rodread/DaisyKiteTurbineControl/2019-11-14_09-22-19.jpg

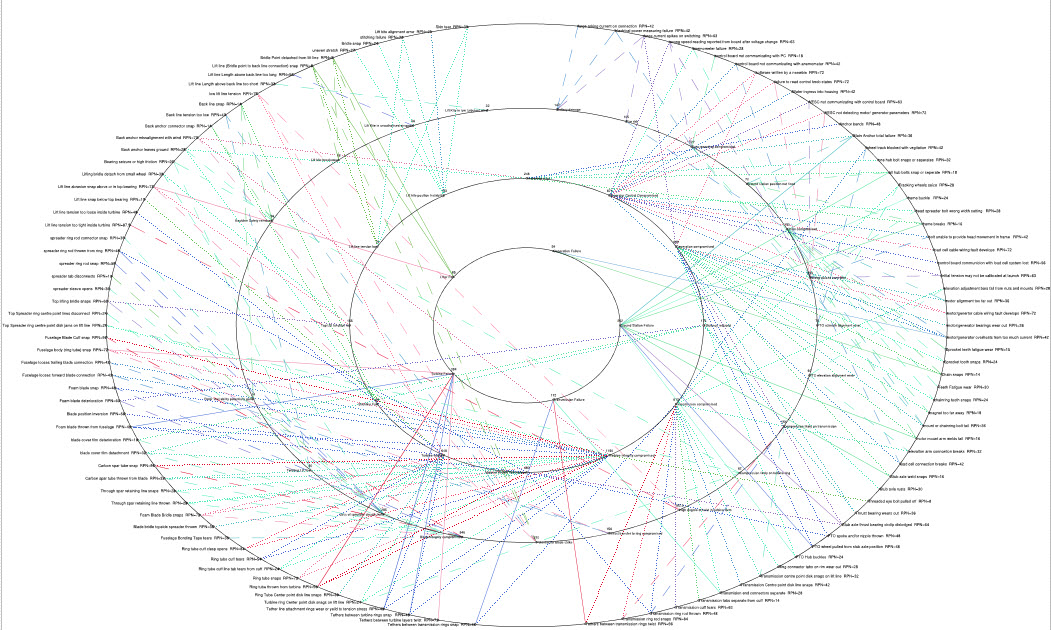
2019-11-14_09-22-19.jpg
