rodread/DaisyKiteTurbineControl/29APR20-Hexring-Tower/buffer.cpp

/*
	Copyright 2012-2014 Benjamin Vedder	benjamin@vedder.se

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
    You should have received a copy of the GNU General Public License
    along with this program.  If not, see <http://www.gnu.org/licenses/>.
    */

/*
 * buffer.c
 *
 *  Created on: 13 maj 2013
 *      Author: benjamin
 */

#include "buffer.h"

void buffer_append_int16(uint8_t* buffer, int16_t number, int32_t *index) {
	buffer[(*index)++] = number >> 8;
	buffer[(*index)++] = number;
}

void buffer_append_uint16(uint8_t* buffer, uint16_t number, int32_t *index) {
	buffer[(*index)++] = number >> 8;
	buffer[(*index)++] = number;
}

void buffer_append_int32(uint8_t* buffer, int32_t number, int32_t *index) {
	buffer[(*index)++] = number >> 24;
	buffer[(*index)++] = number >> 16;
	buffer[(*index)++] = number >> 8;
	buffer[(*index)++] = number;
}

void buffer_append_uint32(uint8_t* buffer, uint32_t number, int32_t *index) {
	buffer[(*index)++] = number >> 24;
	buffer[(*index)++] = number >> 16;
	buffer[(*index)++] = number >> 8;
	buffer[(*index)++] = number;
}

void buffer_append_float16(uint8_t* buffer, float number, float scale, int32_t *index) {
    buffer_append_int16(buffer, (int16_t)(number * scale), index);
}

void buffer_append_float32(uint8_t* buffer, float number, float scale, int32_t *index) {
    buffer_append_int32(buffer, (int32_t)(number * scale), index);
}

int16_t buffer_get_int16(const uint8_t *buffer, int32_t *index) {
	int16_t res =	((uint16_t) buffer[*index]) << 8 |
					((uint16_t) buffer[*index + 1]);
	*index += 2;
	return res;
}

uint16_t buffer_get_uint16(const uint8_t *buffer, int32_t *index) {
	uint16_t res = 	((uint16_t) buffer[*index]) << 8 |
					((uint16_t) buffer[*index + 1]);
	*index += 2;
	return res;
}

int32_t buffer_get_int32(const uint8_t *buffer, int32_t *index) {
	int32_t res =	((uint32_t) buffer[*index]) << 24 |
					((uint32_t) buffer[*index + 1]) << 16 |
					((uint32_t) buffer[*index + 2]) << 8 |
					((uint32_t) buffer[*index + 3]);
	*index += 4;
	return res;
}

uint32_t buffer_get_uint32(const uint8_t *buffer, int32_t *index) {
	uint32_t res =	((uint32_t) buffer[*index]) << 24 |
					((uint32_t) buffer[*index + 1]) << 16 |
					((uint32_t) buffer[*index + 2]) << 8 |
					((uint32_t) buffer[*index + 3]);
	*index += 4;
	return res;
}

float buffer_get_float16(const uint8_t *buffer, float scale, int32_t *index) {
    return (float)buffer_get_int16(buffer, index) / scale;
}

float buffer_get_float32(const uint8_t *buffer, float scale, int32_t *index) {
    return (float)buffer_get_int32(buffer, index) / scale;
}

bool buffer_get_bool(const uint8_t *buffer, int32_t *index) {
	
		if (buffer[*index] == 1)
		{
			index++;
			return true;
		}
		else
		{
			index++;
			return false;
		}
		
}

void buffer_append_bool(uint8_t *buffer,bool value, int32_t *index) {

	if (value == true)
	{
		buffer[*index] = 1;
		(*index)++;
	}
	else
	{
		buffer[*index] = 0;
		(*index)++;
	}

}
